flupes/GrannyRoomba/code/org.flupes.ljf.grannyroomba.pctests/src/org/flupes/ljf/grannyroomba/pctests/grannyempty.jpg

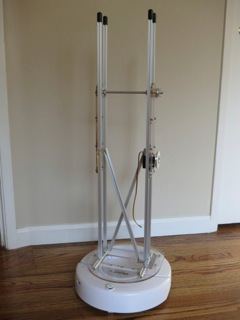
code/org.flupes.ljf.grannyroomba.pctests/src/org/flupes/ljf/grannyroomba/pctests/grannyempty.jpg
