flupes/GrannyRoomba/code/org.flupes.ljf.grannyroomba.pctests/src/org/flupes/ljf/grannyroomba/pctests/KeyboardController.png

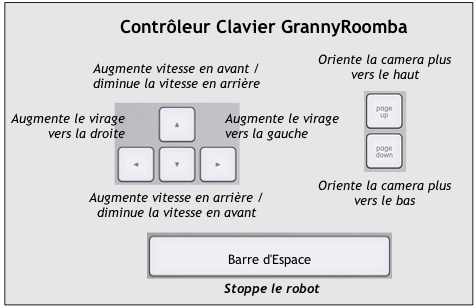
code/org.flupes.ljf.grannyroomba.pctests/src/org/flupes/ljf/grannyroomba/pctests/KeyboardController.png
